Milk-Cool/meshboy/src/rom.h

#pragma once
uint8_t rom[0x4000] = { 255, 255, 255, 255, 255, 255, 255, 255, 255, 255, 255, 255, 255, 255, 255, 255, 255, 255, 255, 255, 255, 255, 255, 255, 255, 255, 255, 255, 255, 255, 255, 255, 233, 255, 255, 255, 255, 255, 255, 255, 34, 13, 32, 252, 201, 255, 255, 255, 26, 34, 19, 13, 32, 250, 201, 255, 255, 255, 255, 255, 255, 255, 255, 255, 245, 229, 33, 165, 192, 195, 128, 0, 195, 18, 15, 255, 255, 255, 255, 255, 255, 255, 255, 255, 255, 255, 255, 255, 255, 255, 255, 255, 255, 255, 255, 255, 255, 255, 255, 255, 255, 255, 255, 255, 255, 255, 255, 255, 255, 255, 255, 255, 128, 64, 32, 16, 8, 4, 2, 1, 1, 2, 4, 8, 16, 32, 64, 128, 197, 213, 42, 182, 40, 11, 229, 58, 110, 103, 231, 225, 35, 24, 243, 232, 4, 209, 193, 225, 240, 65, 230, 2, 32, 250, 241, 217, 33, 163, 192, 52, 32, 2, 35, 52, 62, 1, 224, 145, 195, 128, 255, 240, 65, 230, 2, 32, 250, 62, 192, 195, 132, 255, 175, 1, 41, 0, 33, 160, 192, 205, 40, 5, 62, 192, 224, 146, 103, 175, 111, 14, 160, 195, 40, 0, 243, 224, 255, 175, 251, 224, 15, 201, 240, 146, 183, 200, 224, 70, 62, 40, 61, 32, 253, 201, 255, 255, 255, 255, 255, 255, 255, 255, 255, 255, 255, 255, 255, 255, 255, 255, 201, 255, 255, 255, 195, 166, 5, 255, 255, 255, 255, 255, 255, 255, 255, 255, 24, 85, 255, 255, 206, 237, 102, 102, 204, 13, 0, 11, 3, 115, 0, 131, 0, 12, 0, 13, 0, 8, 17, 31, 136, 137, 0, 14, 220, 204, 110, 230, 221, 221, 217, 153, 187, 187, 103, 99, 110, 14, 236, 204, 221, 220, 153, 159, 187, 185, 51, 62, 0, 0, 0, 0, 0, 0, 0, 0, 0, 0, 0, 0, 0, 0, 0, 0, 4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
